CentyLab/PicoPD_Pro/Document/Back Render.png

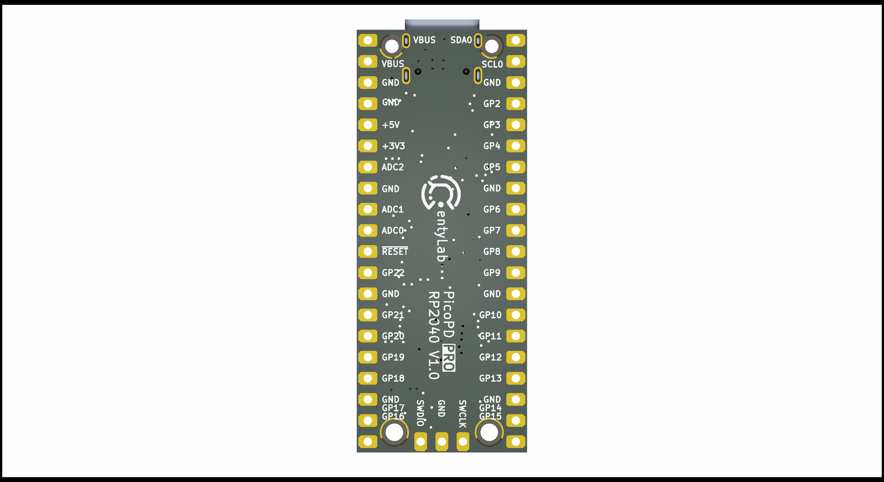
Document/Back Render.png
