CentyLab/PicoPD_Pro/Document/compare_table.png

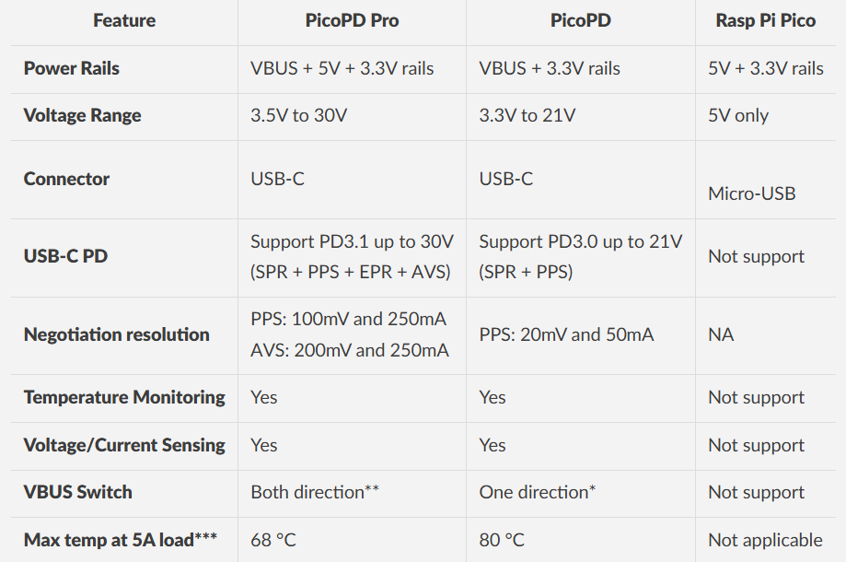
Document/compare_table.png
