CentyLab/PicoPD_Pro/Document/doc7.png

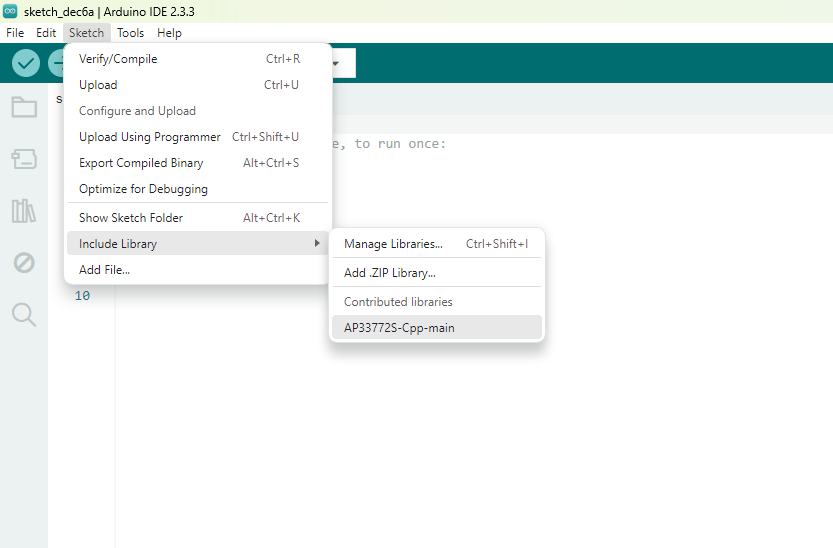
Document/doc7.png
