CentyLab/PicoPD_Pro/Document/Media/Back.JPG

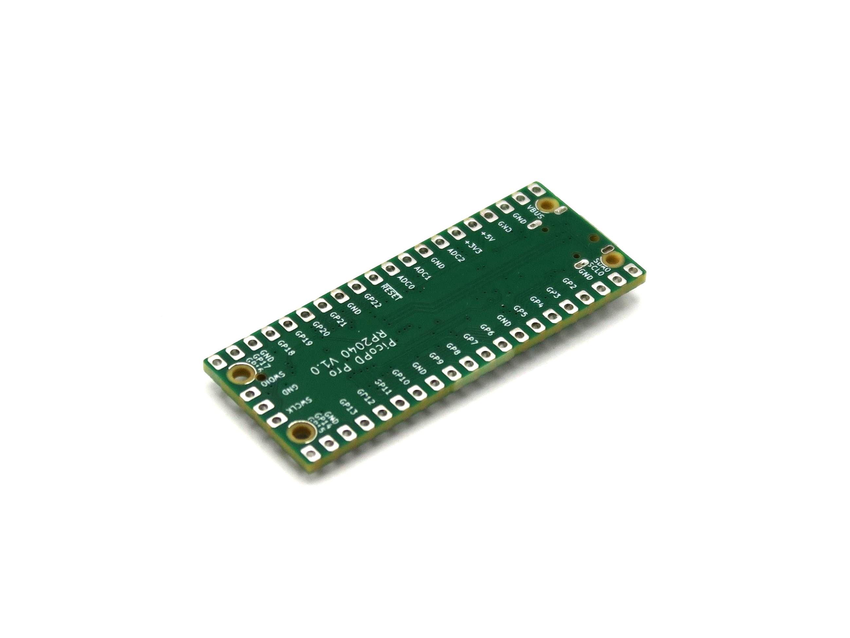
Document/Media/Back.JPG
