CentyLab/PicoPD_Pro/Document/Render.png

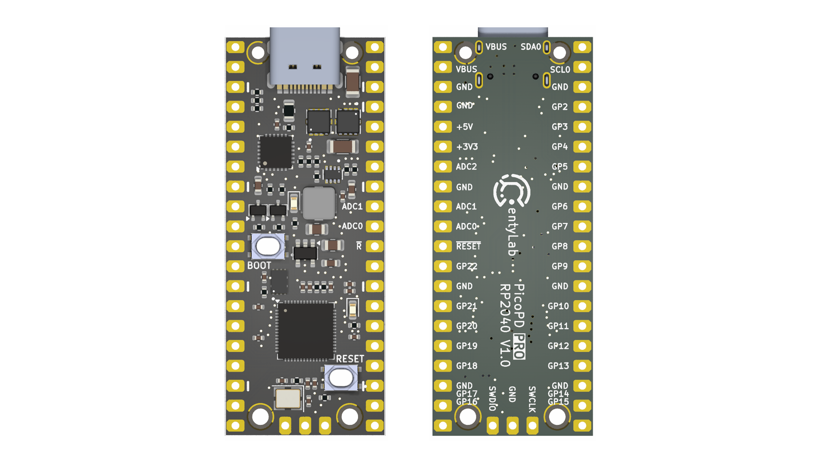
Document/Render.png
